TraditionalSockwearer/Camera-Switching-Macropad/Firmware/CircuitPythonFirmware/movie_data.py

FRAMES = [
    b'\x00\x00\x00\x00\x00\x00\x00\x00\x00\x00\x00\x00\x1f\xff\xff\xf8\x13\x00\x00\xc8\x13\x00\x00\xc8\x1f\x00\x00\xf8\x13\x00\x00\xc8\x13\x00\x00\xc8\x1f\x00\x00\xf8\x13\x00\x00\xc8\x13\x00\x00\xc8\x1f\x00\x00\xf8\x13\x00\x00\xc8\x13\x00\x00\xc8\x1f\xff\xff\xf8\x1f\xff\xff\xf8\x13\x00\x00\xc8\x13\x00\x00\xc8\x1f\x00\x00\xf8\x13\x00\x00\xc8\x13\x00\x00\xc8\x1f\x00\x00\xf8\x13\x00\x00\xc8\x13\x00\x00\xc8\x1f\x00\x00\xf8\x13\x00\x00\xc8\x13\x00\x00\xc8\x1f\xff\xff\xf8\x00\x00\x00\x00\x00\x00\x00\x00\x00\x00\x00\x00',
    b'\x00\x00\x00\x00\x00\x00\x00\x00\x00\x00\x00\x00\x1f\xff\xff\xf8\x13\x00\x00\xc8\x13\x00\x00\xc8\x1f\x00\x00\xf8\x13\x00\x00\xc8\x13\x00\x00\xc8\x1f\x00\x00\xf8\x13\x00\x00\xc8\x13\x00\x00\xc8\x1f\x00\x00\xf8\x13\x00\x00\xc8\x13\x00\x00\xc8\x1f\x00\x00\xf8\x13\x00\x00\xc8\x13\x00\x00\xc8\x1f\xff\xff\xf8\x1f\xff\xff\xf8\x13\x00\x00\xc8\x13\x00\x00\xc8\x1f\x00\x00\xf8\x13\x00\x00\xc8\x13\x00\x00\xc8\x1f\x00\x00\xf8\x13\x00\x00\xc8\x13\x00\x00\xc8\x1f\x00\x00\xf8\x13\x00\x00\xc8\x13\x00\x00\xc8\x1f\xff\xff\xf8\x00\x00\x00\x00\x00\x00\x00\x00\x00\x00\x00\x00',
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
]
